hackersbadge/jingqi2019/src/package/utils/jd-jingqi/files/www/res/ditu.png

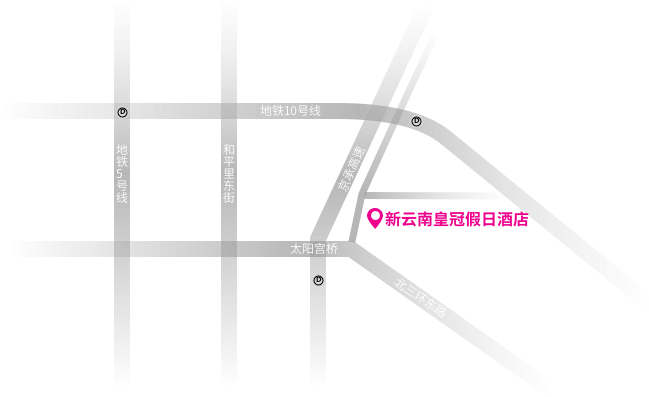
src/package/utils/jd-jingqi/files/www/res/ditu.png
