hackersbadge/jingqi2019/src/package/utils/jd-jingqi/files/www/res/zhubiaot.jpg

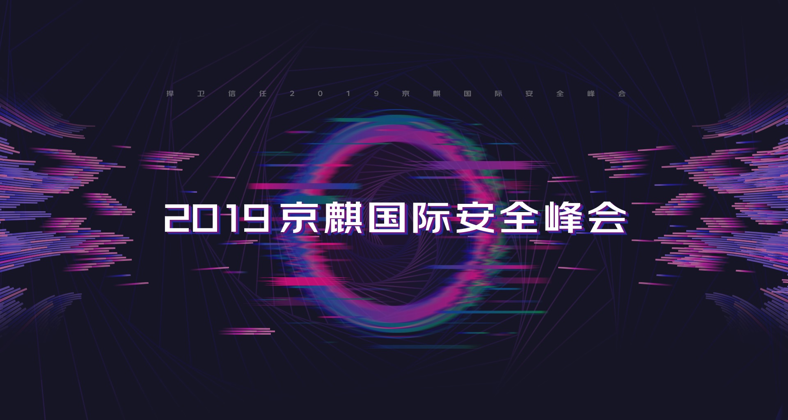
src/package/utils/jd-jingqi/files/www/res/zhubiaot.jpg
